PingguSoft/HexaPodMega/Schematic/ArduinoMega/bt_serial.png

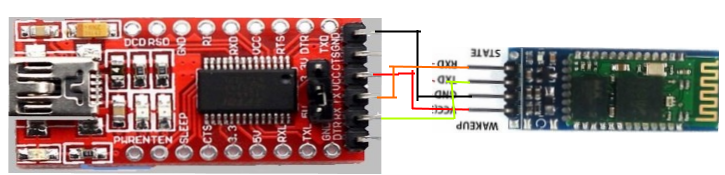
Schematic/ArduinoMega/bt_serial.png
