PingguSoft/HexaPodMega/Schematic/ArduinoMega/bt_setting.png

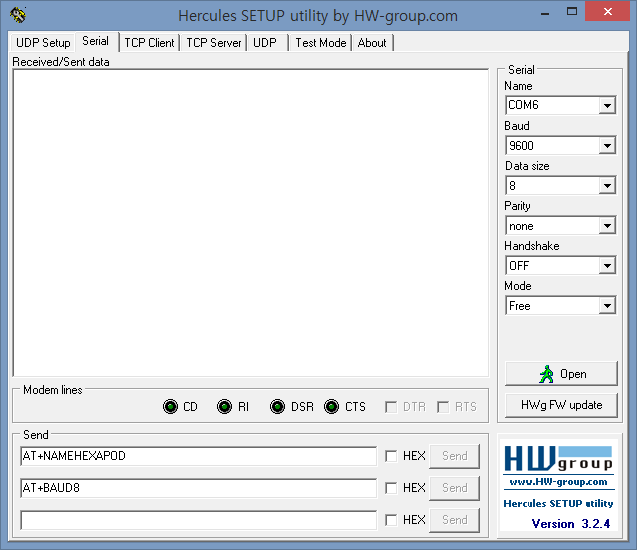
Schematic/ArduinoMega/bt_setting.png
