PingguSoft/HexaPodMega/Schematic/ArduinoMega/connection.png

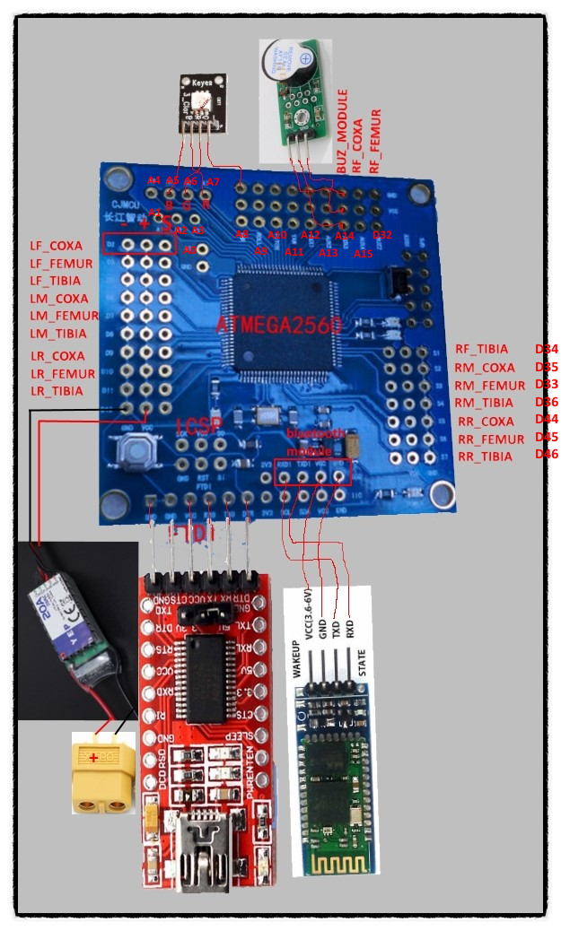
Schematic/ArduinoMega/connection.png
