PingguSoft/HexaPodMega/Schematic/ServoController/option_cal.png

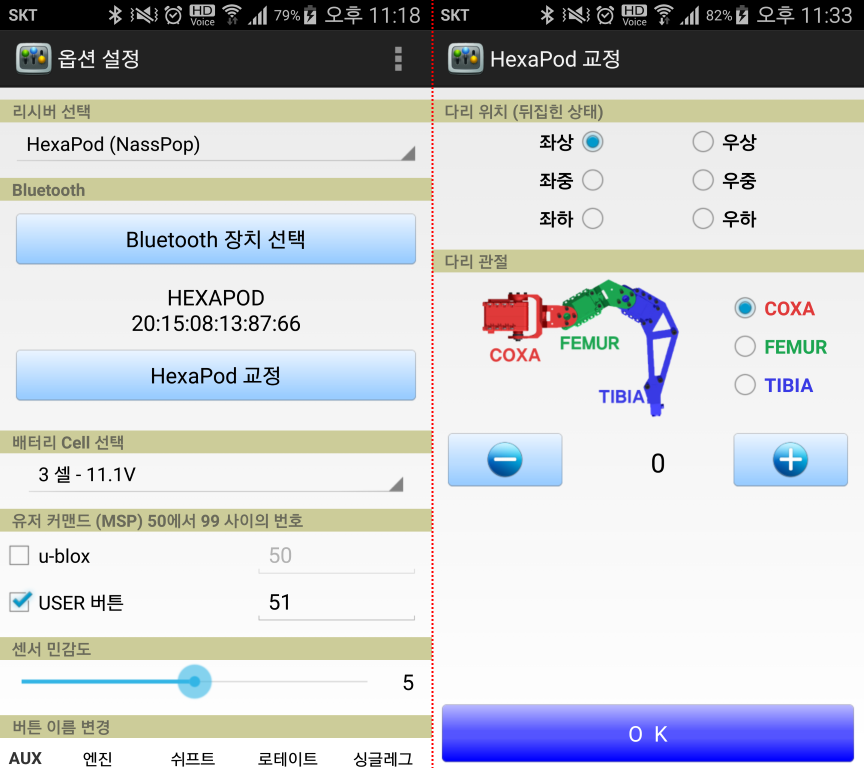
Schematic/ServoController/option_cal.png
