PingguSoft/HexaPodMega/Schematic/ServoController/servo_controller.jpg

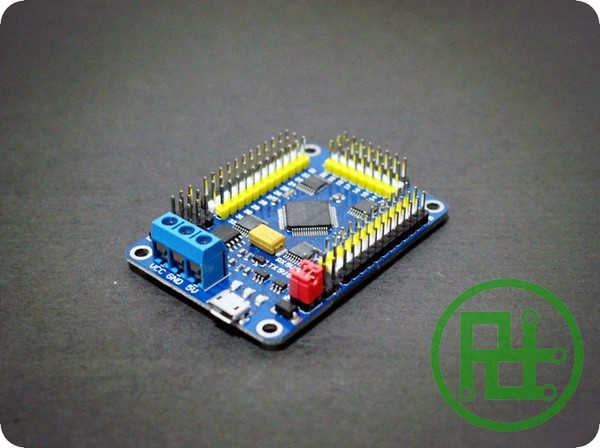
Schematic/ServoController/servo_controller.jpg
