PingguSoft/HexaPodMega/source/PhoenixServoUSC.h

/*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
 This program is distributed in the hope that it will be useful,
 but WITHOUT ANY WARRANTY; without even the implied warranty of
 MERCHANTABILITY or FITNESS FOR A PARTICULAR PURPOSE.  See the
 GNU General Public License for more details.
 see <http://www.gnu.org/licenses/>
*/

#ifndef _PHOENIX_SERVO_USC_H_
#define _PHOENIX_SERVO_USC_H_
#include <SoftwareSerial.h>
#include "config.h"
#include "utils.h"
#include "ServoEx.h"
#include "PhoenixServo.h"


class PhoenixServoUSC : public PhoenixServo
{
private:
#if defined(CONFIG_SERVO_USC_TX) && defined(CONFIG_CPU_PROMINI)
    SoftwareSerial  *mSerial;
#else
    HardwareSerial  *mSerial;
#endif
    u8              mServos[CONFIG_NUM_LEGS * CONFIG_DOF_PER_LEG];
    s16             mServoOffsets[CONFIG_NUM_LEGS * CONFIG_DOF_PER_LEG];
    u16             mServoValues[CONFIG_NUM_LEGS][CONFIG_DOF_PER_LEG];
    bool            mBoolServosAttached;

    u16             mVoltBuf[CONFIG_VBAT_SMOOTH];
    u16             mVoltSum;
    u8              mVoltIdx;

    void loadServosConfig(void);
    void attachServos(void);
    void setLegs1500ms(void);
    void handleServoOffsets(void);

#if (CONFIG_DOF_PER_LEG == 4)
    void writeServo(u8 leg, u16 wCoxa, u16 wFemur, u16 wTibia, u16 wTars);
#else
    void writeServo(u8 leg, u16 wCoxa, u16 wFemur, u16 wTibia);
#endif


public:
    PhoenixServoUSC(void);
    PhoenixServoUSC(HardwareSerial *serial);

    virtual void init(void);
    virtual void start(void);
    virtual void commit(u16 wMoveTime);
    virtual void release(void);
#if (CONFIG_DOF_PER_LEG == 4)
    virtual void write(u8 LegIndex, s16 sCoxaAngle1, s16 sFemurAngle1, s16 sTibiaAngle1, s16 sTarsAngle1);
#else
    virtual void write(u8 LegIndex, s16 sCoxaAngle1, s16 sFemurAngle1, s16 sTibiaAngle1);
#endif
    virtual u8   getBattVolt(void);

#ifdef CONFIG_TERMINAL
    virtual void showTerminal(void);
    virtual bool handleTerminal(u8 *psz, u8 bLen);
    void move(int servo, int val, unsigned int time);
#endif

};

#endif
