PingguSoft/HexaPodMega/source/ServoTest/ServoTest.ino

#include <SoftwareSerial.h>
#include <Servo.h> 

Servo   servoLR;

void setup() 
{ 
	Serial.begin(115200);
	while (!Serial) {
		; // wait for serial port to connect. Needed for Leonardo only
	}
	servoLR.attach(2);
} 

void loop() 
{ 
    int pos;
    
    for(pos = 0; pos < 180; pos++) {
        servoLR.write(pos);
        delay(15);
    }
    for(pos = 180; pos > 0; pos--) {
        servoLR.write(pos);
        delay(15);
    }
    servoLR.write(90);

    for(;;);
}
